jankurnicki/ESP32_full_board/footprints/MCP73871-4CCI_ML.step

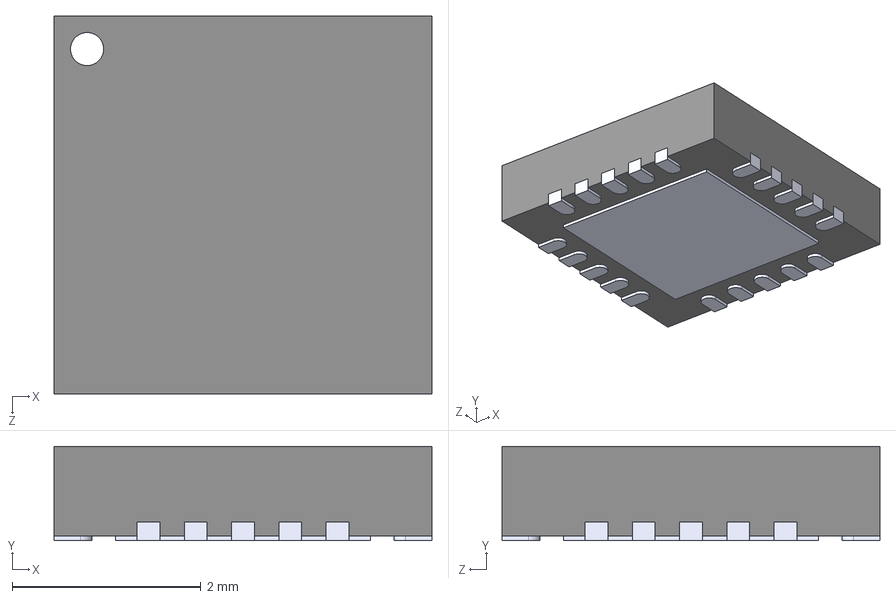
[picture p18: CAD file, 2026-09-22]
footprints/MCP73871-4CCI_ML.step
4.00 x 1.00 x 4.00 mm
