jankurnicki/ESP32_full_board/footprints/GSD090012SEU.step

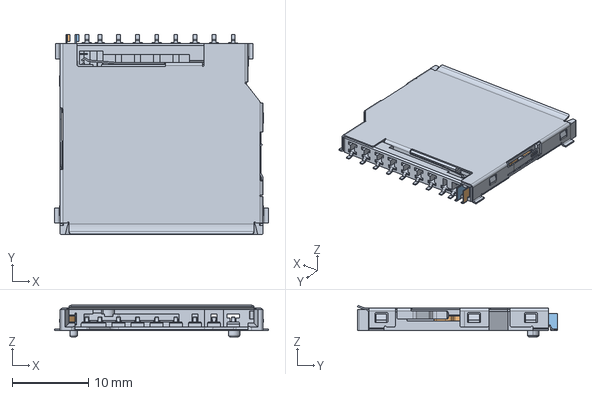
[picture p19: CAD file, 2026-09-22]
footprints/GSD090012SEU.step
28.0 x 26.2 x 4.13 mm
